wuspy/portal_calendar/resources/error.gif

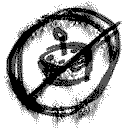
resources/error.gif
