wuspy/portal_calendar/global.h

#include <Arduino.h>
#include "config.h"

#ifndef PORTALCALENDAR_GLOBAL_H
#define PORTALCALENDAR_GLOBAL_H

#define uS_PER_S 1000000
#define SECONDS_PER_HOUR 3600
#define SECONDS_PER_DAY (SECONDS_PER_HOUR * 24)

#define clamp(x, y) min(max(x, -y), y)

// Translate configured times to units the code uses
#define ERROR_RETRY_INTERVAL_SECONDS            ERROR_RETRY_INTERVAL_MINUTES * 60
#define ERROR_AFTER_SECONDS_WITHOUT_INTERNET    ERROR_AFTER_HOURS_WITHOUT_INTERNET * 3600
#define SECONDS_BEFORE_MIDNIGHT_TO_SYNC_1       MINUTES_BEFORE_MIDNIGHT_TO_SYNC_1 * 60
#define SECONDS_BEFORE_MIDNIGHT_TO_SYNC_2       MINUTES_BEFORE_MIDNIGHT_TO_SYNC_2 * 60
#define TZ_LOOKUP_TIMEOUT_MS                    TZ_LOOKUP_TIMEOUT_SECONDS * 1000
#define NTP_TIMEOUT_MS                          NTP_TIMEOUT_SECONDS * 1000
#define WIFI_CONNECTION_TIMEOUT_MS              WIFI_CONNECTION_TIMEOUT_SECONDS * 1000

#endif // PORTALCALENDAR_GLOBAL_H
