wuspy/portal_calendar/localization.cpp

#include "localization.h"

const Locale getLocale(String code)
{
    for (Locale locale: LOCALES) {
        if (code.equals(locale.code)) {
            return locale;
        }
    }
    if (code.equals(DEFAULT_LOCALE)) {
        log_e("Default locale '" DEFAULT_LOCALE "' not found!");
        return LOCALES[0];
    }
    log_e("Locale '%s' not found, returning default locale '" DEFAULT_LOCALE "'", code.c_str());
    return getLocale(DEFAULT_LOCALE);
}
